MarkChuCarroll/simplex-tenor/mtenor-out-body-center.stl

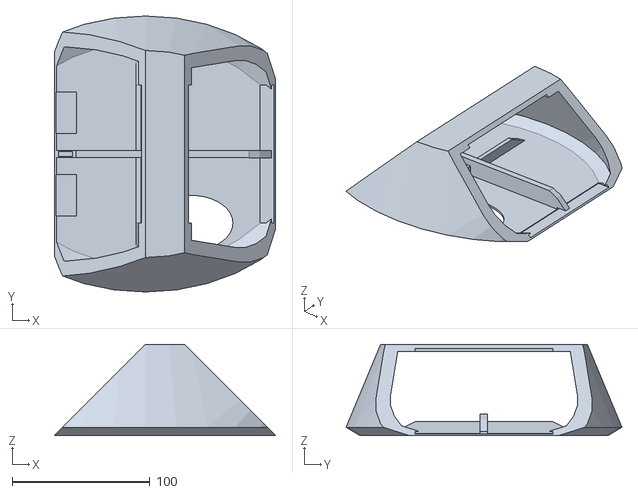
[picture p15: CAD file, 2025-12-02]
mtenor-out-body-center.stl
160.3 x 200.0 x 66.0
