MarkChuCarroll/simplex-tenor/mtenor-out-fretboard-a.stl

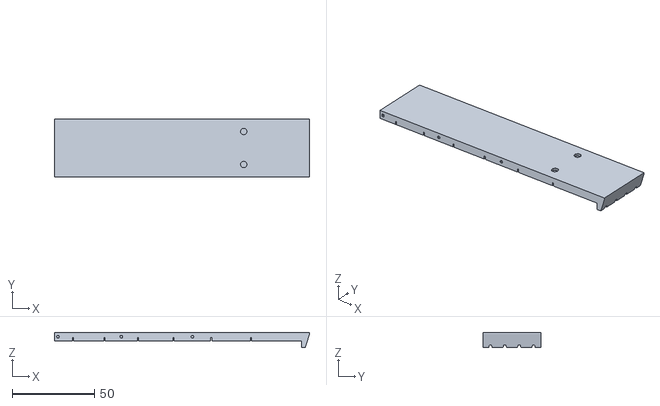
[picture p16: CAD file, 2025-12-02]
mtenor-out-fretboard-a.stl
155.0 x 35.0 x 9.00
